careyi3/ball_and_beam/images/pid_controller.png

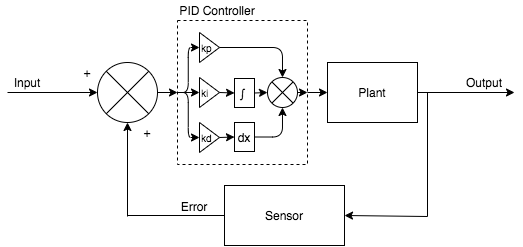
images/pid_controller.png
