careyi3/ball_and_beam/images/rear.jpg

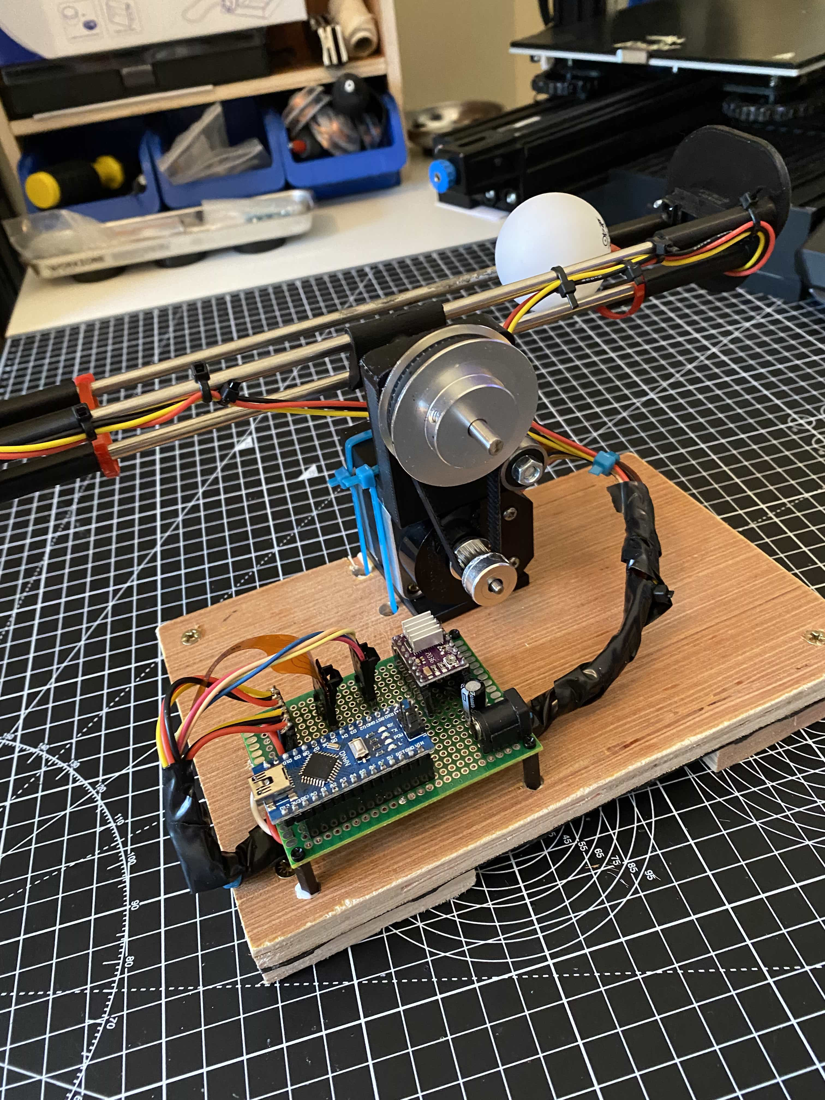
images/rear.jpg
